janelia-idf/arduino_relay_controller/pcb/arduino_relay_control.sch

## KiCad design pcb/arduino_relay_control.sch (2019-02-07)

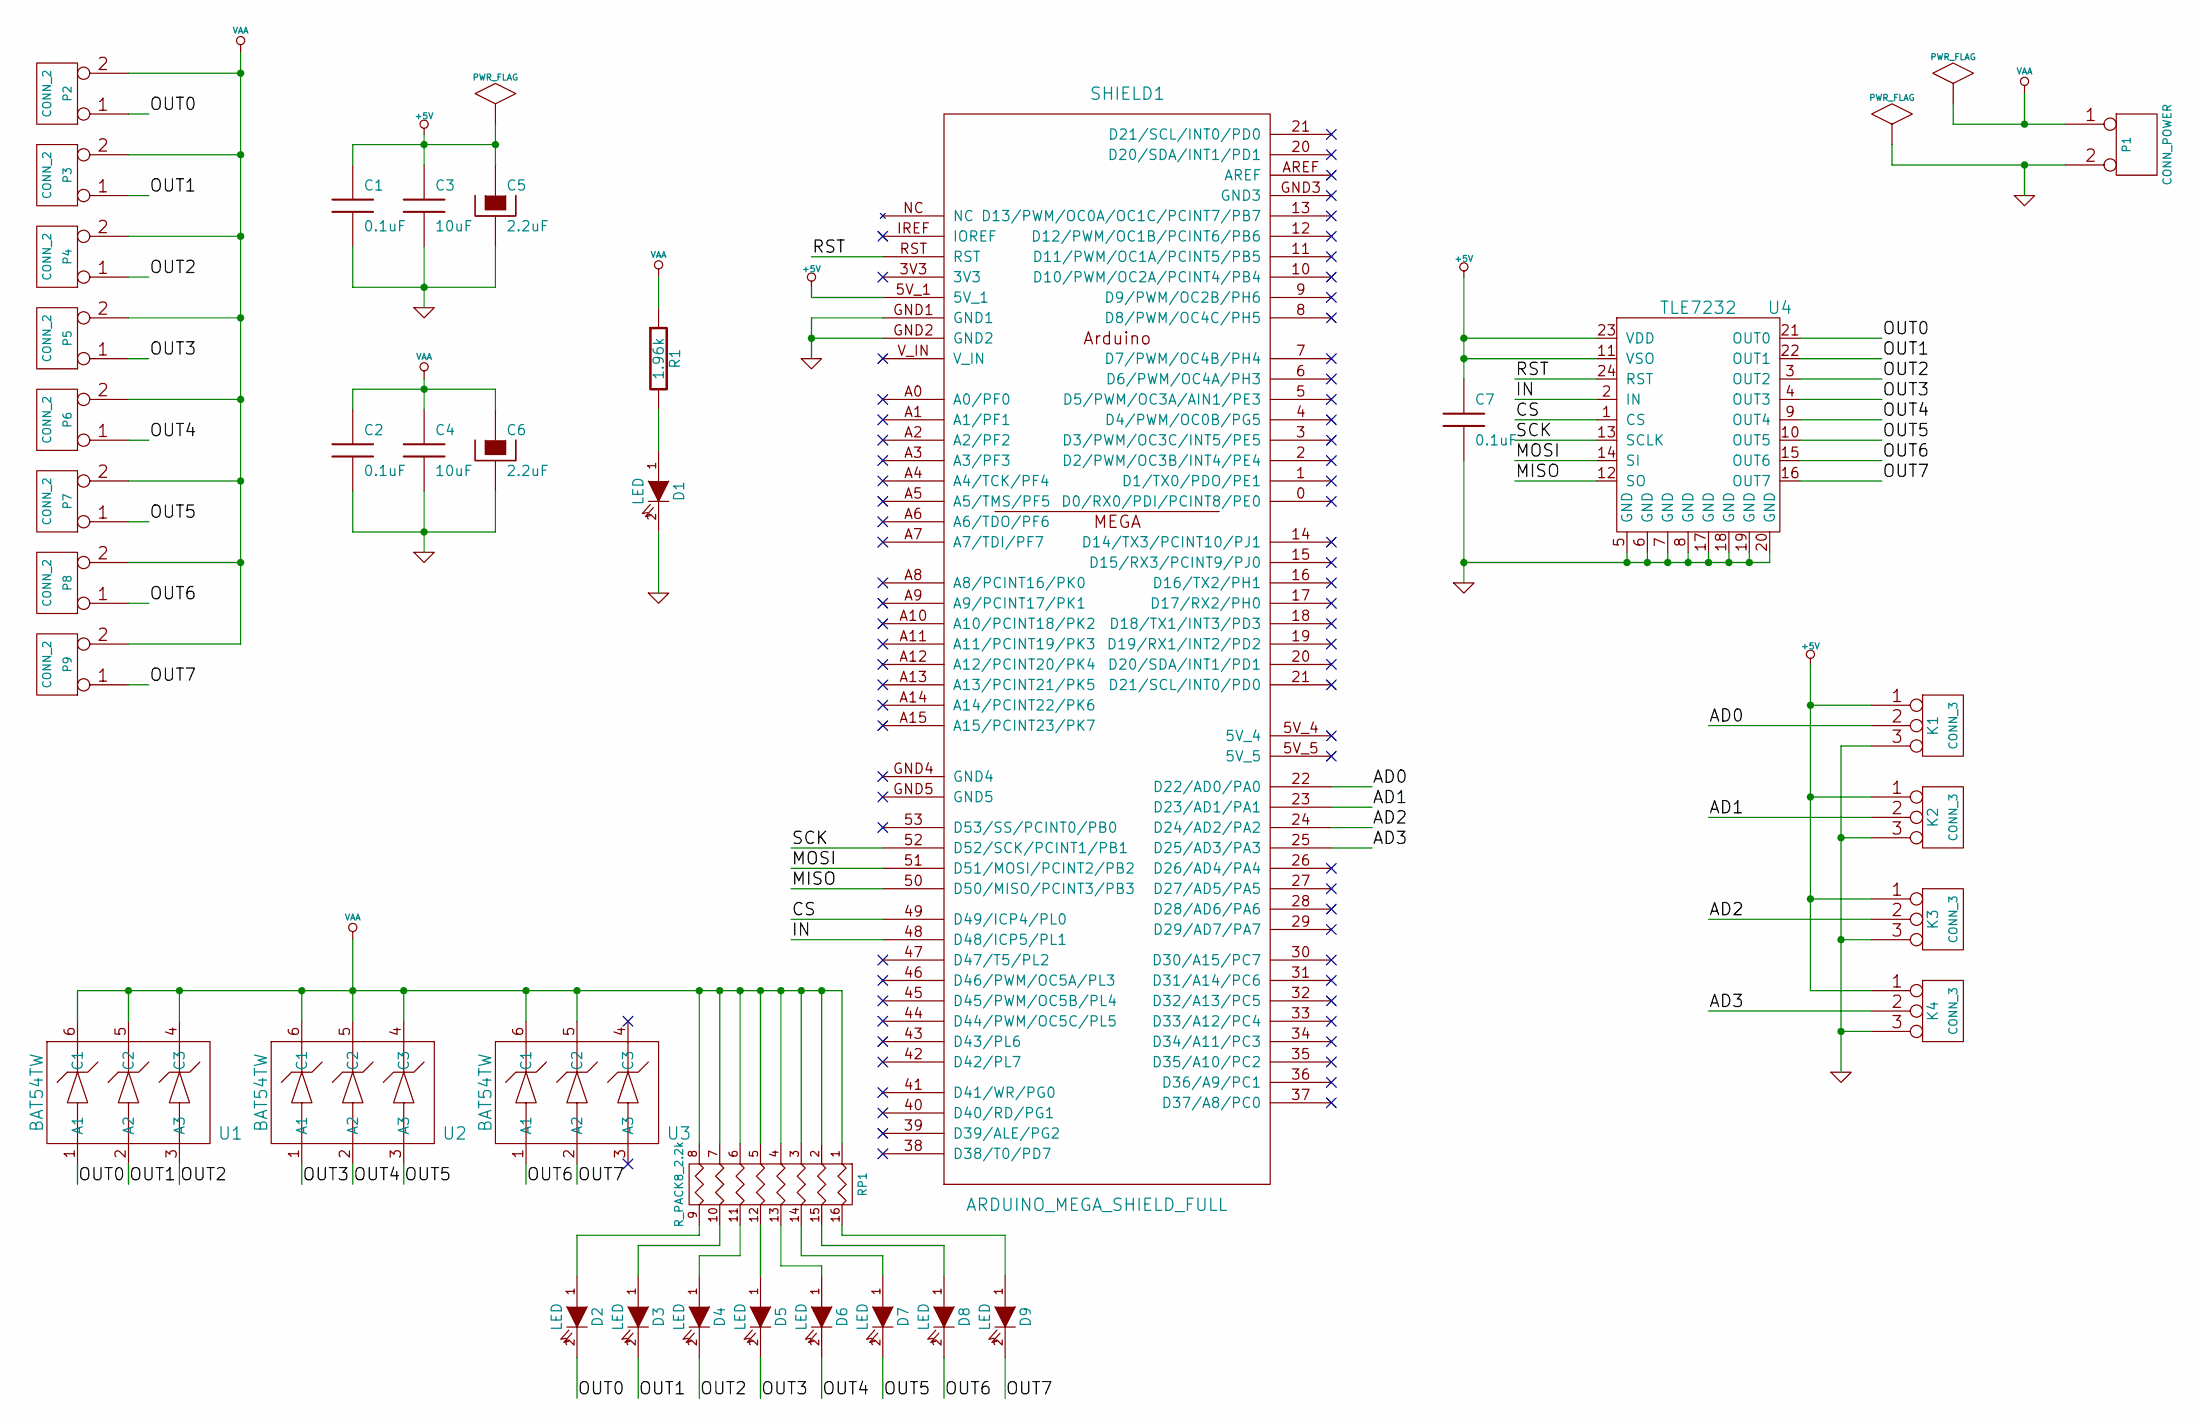
[picture p9: schematic arduino_relay_control.sch]

Parts:
C1, C2, C7: 0.1uF
C3, C4: 10uF
C5, C6: 2.2uF
D1, D2, D3, D4, D5, D6, D7, D8, D9: LED
K1, K2, K3, K4: CONN_3
P1: CONN_POWER
P2, P3, P4, P5, P6, P7, P8, P9: CONN_2
R1: 1.96k
RP1: R_PACK8_2.2k
SHIELD1: ARDUINO_MEGA_SHIELD_FULL
U1, U2, U3: BAT54TW
U4: TLE7232

Connections:
+5V: C1.1, C3.1, C5.1, C7.1, K1.1, K2.1, K3.1, K4.1, SHIELD1.5V_1, U4.11 (VSO), U4.23 (VDD)
AD0: K1.2 (PM), SHIELD1.22 (D22/AD0/PA0)
AD1: K2.2 (PM), SHIELD1.23 (D23/AD1/PA1)
AD2: K3.2 (PM), SHIELD1.24 (D24/AD2/PA2)
AD3: K4.2 (PM), SHIELD1.25 (D25/AD3/PA3)
CS: SHIELD1.49 (D49/ICP4/PL0), U4.1 (CS)
GND: C1.2, C2.2, C3.2, C4.2, C5.2, C6.2, C7.2, D1.2 (K), K1.3, K2.3, K3.3, K4.3, P1.2 (PM), SHIELD1.GND1, SHIELD1.GND2, U4.5 (GND), U4.6 (GND), U4.7 (GND), U4.8 (GND), U4.17 (GND), U4.18 (GND), U4.19 (GND), U4.20 (GND)
IN: SHIELD1.48 (D48/ICP5/PL1), U4.2 (IN)
MISO: SHIELD1.50 (D50/MISO/PCINT3/PB3), U4.12 (SO)
MOSI: SHIELD1.51 (D51/MOSI/PCINT2/PB2), U4.14 (SI)
unnamed: D1.1 (A), R1.2
unnamed: D2.1 (A), RP1.9 (R8)
unnamed: D3.1 (A), RP1.10 (R7)
unnamed: D4.1 (A), RP1.11 (R6)
unnamed: D5.1 (A), RP1.12 (R5)
unnamed: D6.1 (A), RP1.13 (R4)
unnamed: D7.1 (A), RP1.14 (R3)
unnamed: D8.1 (A), RP1.15 (R2)
unnamed: D9.1 (A), RP1.16 (R1)
OUT0: D2.2 (K), P2.1, U1.1 (A1), U4.21 (OUT0)
OUT1: D3.2 (K), P3.1, U1.2 (A2), U4.22 (OUT1)
OUT2: D4.2 (K), P4.1, U1.3 (A3), U4.3 (OUT2)
OUT3: D5.2 (K), P5.1, U2.1 (A1), U4.4 (OUT3)
OUT4: D6.2 (K), P6.1, U2.2 (A2), U4.9 (OUT4)
OUT5: D7.2 (K), P7.1, U2.3 (A3), U4.10 (OUT5)
OUT6: D8.2 (K), P8.1, U3.1 (A1), U4.15 (OUT6)
OUT7: D9.2 (K), P9.1, U3.2 (A2), U4.16 (OUT7)
RST: SHIELD1.RST, U4.24 (RST)
SCK: SHIELD1.52 (D52/SCK/PCINT1/PB1), U4.13 (SCLK)
VAA: C2.1, C4.1, C6.1, P1.1, P2.2 (PM), P3.2 (PM), P4.2 (PM), P5.2 (PM), P6.2 (PM), P7.2 (PM), P8.2 (PM), P9.2 (PM), R1.1, RP1.1, RP1.2, RP1.3, RP1.4, RP1.5, RP1.6, RP1.7, RP1.8, U1.4 (C3), U1.5 (C2), U1.6 (C1), U2.4 (C3), U2.5 (C2), U2.6 (C1), U3.5 (C2), U3.6 (C1)
